russellmcc/switch_vca/simulations/jfet_switch.asc

D1: diode
J1: njf
R1: res; 100k
U2: UniversalOpamp2; Avol=13Meg GBW=13Meg Slew=13Meg
V1: voltage; SINE(0 5 100)
V2: voltage; 5V; Rser=10
V3: voltage; -12V
V4: voltage; PULSE(0 5 0 .000024 0 0 .000024)
V5: voltage; PULSE(0 5 0 .01 .01 0 .02)
Named nets: 0, 5V, -12V, switch
.tran .02
;tran .02
