russellmcc/switch_vca/simulations/sawgen.asc

C1: cap; 100pF
C2: cap; 100pF
M1: pmos
R1: res; 330k
R2: res; 3
R3: res; 10k
U1: UniversalOpamp2; Avol=10Meg GBW=100Meg Slew=100Meg
V1: voltage; 12
V2: voltage; -12
V3: voltage; 5V
Named nets: 0, 12V, -12V, 5V
.tran .01
