russellmcc/switch_vca/simulations/switching_filter.asc

C1: cap; 68pF
C2: cap; 82pF
C3: cap; 27pF
C4: cap; 180pF
R1: res; 100k
R2: res; 100k
R3: res; 100k
R4: res; 100k
U1: LT1001
U2: LT1001
V1: voltage; 12
V2: voltage; 12
V3: voltage; ""; AC 1
V4: voltage; 12
V5: voltage; 12
Named nets: 0, Out
.ac oct 12 20 200000
